waterbearfieldschool/diy-phone/oldbranch/v24/p26.py

# SPDX-FileCopyrightText: 2021 ladyada for Adafruit Industries
# SPDX-License-Identifier: MIT

"""
This test will initialize the display using displayio and draw a solid green
background, a smaller purple rectangle, and some yellow text.
"""
import time
import adafruit_sdcard
import board
import displayio
import digitalio
import storage
import terminalio
import busio
from adafruit_display_text import label
from fourwire import FourWire
from adafruit_bus_device.i2c_device import I2CDevice
from adafruit_st7789 import ST7789
import supervisor
supervisor.runtime.autoreload = False


address_book = [["Don (voip)",16512524765],["Don (iphone)",17813230341],["Liz",16174299144]]

recipient_index=0
recipient=address_book[recipient_index]

# Address book functions
def save_address_book():
    try:
        with open("/sd/addressbook.txt", "w") as f:
            for entry in address_book:
                f.write(f"{entry[0]},{entry[1]}\n")
        pass  # Address book saved
    except Exception as e:
        pass  # Error saving address book

def load_address_book():
    global address_book
    try:
        with open("/sd/addressbook.txt", "r") as f:
            address_book = []
            for line in f.readlines():
                if line.strip():
                    parts = line.strip().split(',')
                    if len(parts) == 2:
                        name = parts[0]
                        number = int(parts[1])
                        address_book.append([name, number])
        pass  # Address book loaded
    except Exception as e:
        pass  # Error loading address book, using defaults
        # Create default address book file
        save_address_book()

def lookup_contact_name(phone_number):
    # Clean phone number for comparison
    clean_number = str(phone_number).replace('+', '').replace('-', '').replace(' ', '')
    
    for entry in address_book:
        contact_number = str(entry[1]).replace('+', '').replace('-', '').replace(' ', '')
        if clean_number.endswith(contact_number) or contact_number.endswith(clean_number):
            return entry[0]
    
    # Return formatted phone number if not found
    if clean_number.startswith('1') and len(clean_number) == 11:
        return f"+1 {clean_number[1:4]}-{clean_number[4:7]}-{clean_number[7:]}"
    elif len(clean_number) == 10:
        return f"{clean_number[:3]}-{clean_number[3:6]}-{clean_number[6:]}"
    else:
        return clean_number

# Removed search_contacts function - no longer needed

spi = busio.SPI(board.SCK, board.MOSI, board.MISO)
cs = digitalio.DigitalInOut(board.D10)

sdcard = adafruit_sdcard.SDCard(spi, cs)
vfs = storage.VfsFat(sdcard)
storage.mount(vfs, "/sd")
    
with open("/sd/test.txt", "w") as f:
    f.write("Hello world!\r\n")

with open("/sd/test.txt", "r") as f:
    pass  # File test
    
    
# Release any resources currently in use for the displays
displayio.release_displays()

#spi = board.SPI()
spi = busio.SPI(clock=board.A2, MOSI=board.A0, MISO=board.A1)
tft_cs = board.A3
tft_dc = board.A5

display_bus = FourWire(spi, command=tft_dc, chip_select=tft_cs, reset=board.D12)

display = ST7789(display_bus, width=320, height=240, rotation=90)

# Make the display context
splash = displayio.Group()
display.root_group = splash

#color_bitmap = displayio.Bitmap(320, 240, 1)
#color_palette = displayio.Palette(1)
#color_palette[0] = 0x00FF00  # Bright Green

#bg_sprite = displayio.TileGrid(color_bitmap, #pixel_shader=color_palette, x=0, y=0)
#splash.append(bg_sprite)

# Draw a smaller inner rectangle
#inner_bitmap = displayio.Bitmap(280, 200, 1)
#inner_palette = displayio.Palette(1)
#inner_palette[0] = 0xAA0088  # Purple
#inner_sprite = displayio.TileGrid(inner_bitmap, #pixel_shader=inner_palette, x=20, y=20)
#splash.append(inner_sprite)

# Draw a label
#text_group = displayio.Group(scale=1, x=57, y=120)
#text = "Hello World!"
#text_area = label.Label(terminalio.FONT, text=text, color=0xFFFF00)
#text_group.append(text_area)  # Subgroup for text scaling
#splash.append(text_group)

#recipient_area = label.Label(terminalio.FONT, text="", color=0xFFFF00, x=5, y=5)

# Inbox view elements
inbox_title = label.Label(terminalio.FONT, text="INBOX", color=0x00FF00, scale=2, x=5, y=10)
status_area = label.Label(terminalio.FONT, text="", color=0xFFFF00, scale=1, x=5, y=220)
info_area = label.Label(terminalio.FONT, text="", color=0x888888, scale=1, x=5, y=230)

# Message list lines (showing multiple messages in inbox view)
msg_line1 = label.Label(terminalio.FONT, text="", color=0xFFFF00, scale=1, x=5, y=35)
msg_line2 = label.Label(terminalio.FONT, text="", color=0xFFFF00, scale=1, x=5, y=50)  
msg_line3 = label.Label(terminalio.FONT, text="", color=0xFFFF00, scale=1, x=5, y=65)
msg_line4 = label.Label(terminalio.FONT, text="", color=0xFFFF00, scale=1, x=5, y=80)
msg_line5 = label.Label(terminalio.FONT, text="", color=0xFFFF00, scale=1, x=5, y=95)
msg_line6 = label.Label(terminalio.FONT, text="", color=0xFFFF00, scale=1, x=5, y=110)
msg_line7 = label.Label(terminalio.FONT, text="", color=0xFFFF00, scale=1, x=5, y=125)
msg_line8 = label.Label(terminalio.FONT, text="", color=0xFFFF00, scale=1, x=5, y=140)

# Detail view elements (hidden initially)
detail_from = label.Label(terminalio.FONT, text="", color=0x00FF00, scale=1, x=5, y=35)
detail_time = label.Label(terminalio.FONT, text="", color=0x888888, scale=1, x=5, y=50)
detail_content1 = label.Label(terminalio.FONT, text="", color=0xFFFF00, scale=1, x=5, y=70)
detail_content2 = label.Label(terminalio.FONT, text="", color=0xFFFF00, scale=1, x=5, y=85)
detail_content3 = label.Label(terminalio.FONT, text="", color=0xFFFF00, scale=1, x=5, y=100)
detail_content4 = label.Label(terminalio.FONT, text="", color=0xFFFF00, scale=1, x=5, y=115)
detail_content5 = label.Label(terminalio.FONT, text="", color=0xFFFF00, scale=1, x=5, y=130)
detail_actions = label.Label(terminalio.FONT, text="", color=0x00FF00, scale=1, x=5, y=155)

# Compose view elements  
compose_title = label.Label(terminalio.FONT, text="", color=0x00FF00, scale=1, x=5, y=35)
compose_content = label.Label(terminalio.FONT, text="", color=0xFFFF00, scale=1, x=5, y=55)

msg_lines = [msg_line1, msg_line2, msg_line3, msg_line4, msg_line5, msg_line6, msg_line7, msg_line8]
detail_lines = [detail_from, detail_time, detail_content1, detail_content2, detail_content3, detail_content4, detail_content5, detail_actions]
compose_lines = [compose_title, compose_content]

# Add all elements to splash
splash.append(inbox_title)
splash.append(status_area)
splash.append(info_area)

for line in msg_lines:
    splash.append(line)
for line in detail_lines: 
    splash.append(line)
for line in compose_lines:
    splash.append(line)

i2c = board.I2C()

#while not i2c.try_lock():
#    pass
    
#i2c_devices=i2c.scan()
#print(i2c_devices)

#cardkb=95

kb = I2CDevice(i2c, 0x5F)

from adafruit_ticks import ticks_ms, ticks_add, ticks_diff, ticks_less

uart = busio.UART(board.D2, board.A4, baudrate=115200,timeout=0,receiver_buffer_size=5024)

ESC = chr(27)
NUL = '\x00'
CR = "\r"
LF = "\n"
TAB = bytearray(b'\x09')
LEFT = bytearray(b'\xB4')
RIGHT = bytearray(b'\xB7')
DOWN = bytearray(b'\xB6')
UP = bytearray(b'\xB5')
BACK = bytearray(b'\x08')
# Add new keys for inbox navigation
ENTER_KEY = bytearray(b'\r')  # For selecting message
B_KEY = b'b'  # For back
R_KEY = b'r'  # For reply
C_KEY = b'c'  # For compose
N_KEY = b'n'  # For new number entry / get new messages
D_KEY = b'd'  # For delete all from SIM
SPACE_KEY = b' '  # For call screen
DEL_KEY = bytearray(b'\x7f')  # For delete
c = ''
b = bytearray(1)

instr = ''
radio_instr = ''

def parse_sms_message(line):
    if not line.startswith('+CMGL:'):
        return None
    
    try:
        # Parse: +CMGL: index,"status","sender","","timestamp"
        parts = line.split(',')
        
        index = parts[0].split(':')[1].strip()
        status = parts[1].strip().strip('"')
        sender = parts[2].strip().strip('"') 
        
        # Reconstruct timestamp from parts 4 and 5 (it got split by comma)
        timestamp_part1 = parts[4].strip().strip('"')  # "25/12/25"
        timestamp_part2 = parts[5].strip().strip('"')  # "16:25:06-32"
        timestamp = timestamp_part1 + ',' + timestamp_part2
        
        # Convert timestamp to filename-safe format: YYMMDD_HHMMSS
        # From: "25/12/25,16:25:06-32" to: "251225_162506"
        date_part, time_part = timestamp.split(',')
        time_clean = time_part.split('-')[0]
        file_timestamp = date_part.replace('/', '') + '_' + time_clean.replace(':', '')
        
        result = {
            'index': index,
            'status': status, 
            'sender': sender,
            'timestamp': timestamp,
            'file_id': file_timestamp
        }
        return result
    except Exception as e:
        pass  # Error parsing SMS
        return None

def store_sms_to_sd(sms_data, content):
    try:
        filename = f"/sd/sms_{sms_data['file_id']}.txt"
        with open(filename, "w") as f:
            f.write(f"From: {sms_data['sender']}\n")
            f.write(f"Time: {sms_data['timestamp']}\n") 
            f.write(f"Status: {sms_data['status']}\n")
            f.write(f"Content: {content}\n")
        pass  # SMS stored
        return True
    except Exception as e:
        pass  # Error storing SMS
        return False

def load_sms_from_sd(force_reload=False):
    
    sms_list = []
    
    # Try different approaches to find SMS files
    try:
        import os
        files = os.listdir("/sd")
        pass
    except:
        pass  # Manual scan fallback
        # Manual file discovery for CircuitPython
        files = []
        # Try common timestamp patterns based on recent dates
        base_patterns = ["251225", "251226", "251227", "251228", "251229", "251230", "251231"]
        time_patterns = []
        for hour in range(24):
            for minute in range(0, 60, 5):  # Check every 5 minutes
                time_patterns.append(f"{hour:02d}{minute:02d}")
        
        for date in base_patterns[:3]:  # Only check last 3 days
            for time in time_patterns[:20]:  # Reduce to 20 checks
                filename = f"sms_{date}_{time}*.txt"
                try:
                    # Try to open the file to see if it exists
                    test_name = f"sms_{date}_{time}00.txt"
                    with open(f"/sd/{test_name}", "r") as f:
                        files.append(test_name)
                        pass  # Found SMS file
                except:
                    continue
                    
    # Process found files
    for filename in files:
        if filename.startswith("sms_") and filename.endswith(".txt"):
            try:
                filepath = f"/sd/{filename}"
                pass  # Trying to load file
                with open(filepath, "r") as f:
                    lines = f.readlines()
                    if len(lines) >= 4:
                        sms_data = {
                            'filename': filename,
                            'sender': lines[0].strip().replace('From: ', ''),
                            'time': lines[1].strip().replace('Time: ', ''),
                            'status': lines[2].strip().replace('Status: ', ''),
                            'content': lines[3].strip().replace('Content: ', '')
                        }
                        sms_list.append(sms_data)
                        pass  # Successfully loaded
                    else:
                        pass  # Invalid SMS file format
            except Exception as file_error:
                pass  # Error reading file
                
    # Sort by filename (which includes timestamp) - most recent first
    sms_list.sort(key=lambda x: x['filename'], reverse=True)
    
    # Limit to 20 most recent messages to save memory
    if len(sms_list) > 20:
        sms_list = sms_list[:20]
    
    return sms_list

# Global buffer for accumulating SMS notifications
sms_notification_buffer = ""

# Global UART buffer for complete line reading
uart_line_buffer = ""

def read_uart_lines():
    """Read UART data and return complete lines, buffering incomplete data"""
    global uart_line_buffer
    
    if uart.in_waiting > 0:
        # Read all available data
        new_data = uart.read(uart.in_waiting)
        if new_data:
            try:
                # Add to buffer
                uart_line_buffer += new_data.decode()
                
                # Extract complete lines
                lines = []
                while '\r\n' in uart_line_buffer:
                    line, uart_line_buffer = uart_line_buffer.split('\r\n', 1)
                    if line:  # Don't add empty lines
                        lines.append(line)
                
                return lines
                
            except Exception as e:
                print(f"Error reading UART: {e}")
                return []
    
    return []

def handle_incoming_sms_notification(data):
    """Handle +CMTI notification for new incoming SMS"""
    global sms_notification_buffer
    
    try:
        # Decode without keyword arguments (CircuitPython compatibility)
        data_str = data.decode()
        pass  # SMS notification received
        
        # Accumulate data in buffer since notifications can be split
        sms_notification_buffer += data_str
        pass  # Buffer updated
        
        # Check if we have a complete CMTI notification 
        # Look for the reassembled +CMTI pattern with comma and line ending
        if ('CMTI:' in sms_notification_buffer or '+CMTI:' in sms_notification_buffer) and ',' in sms_notification_buffer and '\r\n' in sms_notification_buffer:
            print("Found complete CMTI notification")
            
            # Try to find and reconstruct the CMTI line
            buffer_clean = sms_notification_buffer.replace('\r\n', ' ').replace('\r', ' ').replace('\n', ' ')
            
            # Look for the CMTI pattern - might be split as +C MTI: or +CMTI:
            if 'MTI:' in buffer_clean:
                # Find the MTI: part and reconstruct
                parts = buffer_clean.split()
                cmti_line = None
                
                for i, part in enumerate(parts):
                    if 'MTI:' in part:
                        # Try to reconstruct +CMTI: line
                        if i > 0 and parts[i-1].endswith('+C'):
                            # Case: ['+C', 'MTI:', '"SM",9']
                            cmti_line = '+CMTI: ' + ' '.join(parts[i+1:])
                        elif part.startswith('+') or part.startswith('MTI:'):
                            # Case: ['MTI:', '"SM",9'] or ['+MTI:', '"SM",9']
                            if part.startswith('MTI:'):
                                cmti_line = '+C' + part + ' ' + ' '.join(parts[i+1:])
                            else:
                                cmti_line = part + ' ' + ' '.join(parts[i+1:])
                        break
                
                if cmti_line and ',' in cmti_line:
                    pass  # Reconstructed CMTI
                    process_cmti_line(cmti_line)
                    sms_notification_buffer = ""  # Clear after processing
                else:
                    print("Could not reconstruct valid CMTI line")
            else:
                print("No MTI pattern found in buffer")
                
    except Exception as e:
        pass  # Error handling SMS notification

def process_cmti_line(line):
    """Process a complete +CMTI line"""
    try:
        # Parse: +CMTI: "SM",6
        if ':' in line and ',' in line:
            # Split by comma to get the index
            parts = line.split(',')
            if len(parts) >= 2:
                try:
                    # Extract number from second part, removing quotes and whitespace
                    index_part = parts[1].strip().strip('"').strip()
                    message_index = int(index_part)
                    pass  # New SMS at index
                    
                    # Auto-retrieve the new message
                    retrieve_new_message(message_index)
                    
                except ValueError as ve:
                    pass  # Could not parse message index
                    # Fallback: get all messages
                    auto_get_all_messages()
            else:
                pass  # Unexpected CMTI format
                auto_get_all_messages()
        else:
            pass  # Invalid CMTI line format
            
    except Exception as e:
        pass  # Error processing CMTI line

def retrieve_new_message(message_index):
    """Retrieve a specific message by index"""
    try:
        pass  # Retrieving message
        
        # Set text mode
        uart.write(bytes('AT+CMGF=1\r',"ascii"))
        time.sleep(.2)
        uart.read(uart.in_waiting)  # Clear response
        
        # Read the specific message
        uart.write(bytes(f'AT+CMGR={message_index}\r',"ascii"))
        time.sleep(.5)
        data = uart.read(uart.in_waiting).decode()
        pass  # Message response
        
        # Parse and store the message if valid
        lines = data.split('\r\n')
        current_sms = None
        
        for i, line in enumerate(lines):
            if line.startswith('+CMGR:'):
                # Parse message header: +CMGR: "REC UNREAD","+16512524765","","25/12/26,10:30:15-32"
                current_sms = parse_cmgr_message(line)
                pass  # Parsed message header
            elif current_sms and line.strip() and not line.startswith('AT') and not line.startswith('OK'):
                # This is the message content
                if store_sms_to_sd(current_sms, line.strip()):
                    pass  # Stored new message
                    pass  # Cache removed for memory optimization
                    
                    # Update display if in inbox view
                    if current_view == "inbox":
                        refresh_inbox_highlighting()
                        
                break
                
    except Exception as e:
        pass  # Error retrieving message
        # Fallback: get all messages
        auto_get_all_messages()

def parse_cmgr_message(line):
    """Parse +CMGR response format"""
    try:
        pass  # Parsing CMGR line
        # Parse: +CMGR: "REC UNREAD","+16512524765","","25/12/25","17:48:42-32"
        parts = line.split(',')
        pass  # CMGR parts parsed
        
        if len(parts) >= 5:
            status = parts[0].split(':')[1].strip().strip('"')
            sender = parts[1].strip().strip('"')
            # Skip parts[2] (usually empty "")
            
            # Reconstruct timestamp from parts 3 and 4 (it gets split by comma)
            timestamp_part1 = parts[3].strip().strip('"')  # "25/12/25"
            timestamp_part2 = parts[4].strip().strip('"')  # "17:48:42-32"
            timestamp = timestamp_part1 + ',' + timestamp_part2
            
            pass  # Extracted CMGR data
            
            # Convert timestamp to filename-safe format
            if ',' in timestamp:
                date_part, time_part = timestamp.split(',')
                time_clean = time_part.split('-')[0]
                file_timestamp = date_part.replace('/', '') + '_' + time_clean.replace(':', '')
            else:
                # Fallback if timestamp format is unexpected
                import time as time_mod
                file_timestamp = str(int(time_mod.time()))
                
            result = {
                'index': 'auto',
                'status': status,
                'sender': sender,
                'timestamp': timestamp,
                'file_id': file_timestamp
            }
            pass  # Created CMGR result
            return result
        elif len(parts) >= 4:
            # Fallback for cases where timestamp might not be split
            status = parts[0].split(':')[1].strip().strip('"')
            sender = parts[1].strip().strip('"')
            timestamp = parts[3].strip().strip('"')
            
            pass  # Extracted CMGR data (fallback)
            
            # Convert timestamp to filename-safe format
            if ',' in timestamp:
                date_part, time_part = timestamp.split(',')
                time_clean = time_part.split('-')[0]
                file_timestamp = date_part.replace('/', '') + '_' + time_clean.replace(':', '')
            else:
                # Fallback if timestamp format is unexpected
                import time as time_mod
                file_timestamp = str(int(time_mod.time()))
                
            result = {
                'index': 'auto',
                'status': status,
                'sender': sender,
                'timestamp': timestamp,
                'file_id': file_timestamp
            }
            pass  # Created CMGR result (fallback)
            return result
        else:
            pass  # Insufficient CMGR parts
            return None
            
    except Exception as e:
        pass  # Error parsing CMGR message
        return None

def auto_get_all_messages():
    """Automatically get all messages (fallback for notification parsing errors)"""
    pass  # Auto-retrieving all messages
    get_messages()
    if current_view == "inbox":
        display_inbox()  # Force full refresh

def delete_all_messages():
    uart.write(bytes('AT+CMGF=1\r',"ascii"))
    time.sleep(.2)
    uart.write(bytes('AT+CMGDA="DEL ALL"\r',"ascii"))
    time.sleep(.5)
    data=uart.read(uart.in_waiting).decode()
    print("Delete result:", data)

def network_status():
    uart.write(bytes('AT+CSQ\r',"ascii"))
    time.sleep(.2)
    data=uart.read(uart.in_waiting).decode()
    pass

def get_messages():
    status_area.text='(checking messages...)'
    pass
    uart.write(bytes('AT+CMGF=1\r',"ascii"))
    time.sleep(.2)
    data=uart.read(uart.in_waiting)
    pass
    
    uart.write(bytes('AT+CMGL=\"ALL\"\r',"ascii"))
    time.sleep(.3)
    data=uart.read(uart.in_waiting).decode()
    pass
    
    # Parse and store new SMS messages
    lines = data.split('\r\n')
    current_sms = None
    messages_stored = 0
    
    for i, line in enumerate(lines):
        if line.startswith('+CMGL:'):
            current_sms = parse_sms_message(line)
        elif current_sms and line.strip() and not line.startswith('AT') and not line.startswith('OK'):
            # This is the message content
            if store_sms_to_sd(current_sms, line.strip()):
                messages_stored += 1
            current_sms = None
    
    pass  # Total messages stored
    if messages_stored > 0:
        pass  # Cache removed for memory optimization
    status_area.text=''
    
    # Refresh inbox display after loading messages
    if current_view == "inbox":
        import gc
        gc.collect()  # Force garbage collection
        display_inbox()

# Global variables for inbox navigation  
current_view = "inbox"  # "inbox", "detail", "compose", "select_recipient", "thread"
selected_message_index = 0
inbox_scroll_offset = 0
compose_message = ""
selected_recipient_index = 0
manual_number_entry = ""
recipient_mode = "contacts"  # "contacts" or "manual"

# Call view variables
call_selected_index = 0
call_manual_number = ""
call_mode = "contacts"  # "contacts" or "manual"
call_in_progress = False
call_status = ""  # "dialing", "connected", "ended", "failed"
call_contact_name = ""
call_start_time = 0
call_end_countdown = 0
call_duration_counter = 0
call_connect_time = 0  # Actual time when call connected
call_next_update = 0  # Next time to update display (1 second intervals)

# Incoming call variables
incoming_call_active = False
incoming_call_answered = False
incoming_caller_number = None
last_clip_caller_id = None  # Store caller ID from most recent +CLIP
ring_detected_time = 0  # Time when first RING was detected

# Thread view variables
thread_messages = []
thread_contact = ""
thread_scroll_offset = 0
thread_selected_index = 0

# Minimal thread cache for functionality (memory optimized)
cached_thread_lines = []
thread_cache_valid = False
thread_cache_contact = ""
thread_message_line_map = []

def hide_all_views():
    # Hide inbox view
    for line in msg_lines:
        line.text = ""
    
    # Hide detail view  
    for line in detail_lines:
        line.text = ""
        
    # Hide compose view
    for line in compose_lines:
        line.text = ""
    
    # Clear info area when switching views
    info_area.text = ""

def format_sender(sender):
    # Use contact name if available, otherwise format phone number
    contact_name = lookup_contact_name(sender)
    if len(contact_name) > 10:  # Truncate long names
        return contact_name[:8] + ".."
    return contact_name

def format_timestamp(timestamp):
    # Convert timestamp to "MM/DD HH:MM" format
    try:
        pass  # Formatting timestamp
        
        # Check if timestamp has time component
        if ',' in timestamp:
            # Full timestamp: "25/12/25,16:25:06-32"
            date_part, time_part = timestamp.split(',')
            time_clean = time_part.split('-')[0][:5]  # HH:MM
        else:
            # Date only: "25/12/25"
            date_part = timestamp
            time_clean = "00:00"  # Default time
            
        # Parse date parts
        date_components = date_part.split('/')
        if len(date_components) == 3:
            # Try different date formats
            if len(date_components[0]) == 2 and len(date_components[2]) == 2:
                # Could be YY/MM/DD or DD/MM/YY
                # Check if first component looks like year (20-30) or day (01-31)
                try:
                    first_num = int(date_components[0])
                    if first_num >= 20 and first_num <= 30:
                        # Likely YY/MM/DD format: "25/12/25" -> year=25, month=12, day=25
                        year, month, day = date_components
                    else:
                        # Likely DD/MM/YY format: "26/12/25" -> day=26, month=12, year=25  
                        day, month, year = date_components
                    
                    return f"{month}/{day} {time_clean}"
                except ValueError:
                    # If parsing numbers fails, use fallback
                    return f"{date_components[1]}/{date_components[0]} {time_clean}"
            else:
                # Fallback: assume middle is month, last is day
                return f"{date_components[1]}/{date_components[2]} {time_clean}"
        else:
            return timestamp[:8]  # Fallback
            
    except Exception as e:
        pass  # Error formatting timestamp
        return timestamp[:8] if len(timestamp) >= 8 else timestamp  # Fallback

def format_content_preview(content, max_length=15):
    # Truncate content for inbox preview (shorter to fit 3 columns)
    if len(content) > max_length:
        return content[:max_length] + "..."
    return content

def display_inbox():
    global selected_message_index, inbox_scroll_offset
    import gc
    gc.collect()  # Clear memory before display operations
    hide_all_views()
    
    # Reset title to INBOX and normalize text scales
    inbox_title.text = "INBOX"
    compose_title.scale = 1
    compose_content.scale = 1
    
    sms_list = load_sms_from_sd()
    
    if not sms_list:
        msg_lines[0].text = "No messages"
        pass  # No messages to display
        return
    
    # Ensure selected index is valid
    if selected_message_index >= len(sms_list):
        selected_message_index = len(sms_list) - 1
    elif selected_message_index < 0:
        selected_message_index = 0
    
    # Adjust scroll offset to keep selected message visible
    if selected_message_index < inbox_scroll_offset:
        inbox_scroll_offset = selected_message_index
    elif selected_message_index >= inbox_scroll_offset + len(msg_lines):
        inbox_scroll_offset = selected_message_index - len(msg_lines) + 1
    
    # Display messages in 3-column format: "From | Time | Content"
    for i, line in enumerate(msg_lines):
        msg_idx = inbox_scroll_offset + i
        if msg_idx < len(sms_list):
            sms = sms_list[msg_idx]
            sender = format_sender(sms['sender'])
            timestamp = format_timestamp(sms['time'])
            content = format_content_preview(sms['content'])
            
            # Format: "NAME     TIME     CONTENT..."
            # Use fixed width columns: 10 chars name, 11 chars time, rest content
            sender_col = sender[:10]  # Pad and truncate to 10 chars
            time_col = timestamp[:8]  # Pad and truncate to 11 chars
            
            # Highlight selected message
            if msg_idx == selected_message_index:
                line.text = ">" + sender_col + " " + time_col + " " + content
                line.color = 0x00FF00  # Green for selected
            else:
                line.text = " " + sender_col + " " + time_col + " " + content
                line.color = 0xFFFF00  # Yellow for normal
        else:
            line.text = ""
    
    status_area.text = f"MSG {selected_message_index + 1}/{len(sms_list)} - UP/DN:nav RIGHT/ENTER:view C:compose N:new D:del"
    info_area.text = "↑↓:select  ENTER:thread  C:compose  SPACE:call  N:refresh  D:del  0-9:dial"

def refresh_inbox_highlighting():
    global selected_message_index, inbox_scroll_offset
    
    # Load SMS data from SD card
    sms_list = load_sms_from_sd()
    
    if not sms_list:
        return
    
    # Ensure selected index is valid
    if selected_message_index >= len(sms_list):
        selected_message_index = len(sms_list) - 1
    elif selected_message_index < 0:
        selected_message_index = 0
    
    # Adjust scroll offset with page up/down behavior
    if selected_message_index < inbox_scroll_offset:
        # Scrolling up beyond top - do page up
        inbox_scroll_offset = max(0, selected_message_index - len(msg_lines) + 1)
    elif selected_message_index >= inbox_scroll_offset + len(msg_lines):
        # Scrolling down beyond bottom - do page down
        inbox_scroll_offset = selected_message_index
    
    # Only update highlighting, don't rebuild content
    for i, line in enumerate(msg_lines):
        msg_idx = inbox_scroll_offset + i
        if msg_idx < len(sms_list):
            sms = sms_list[msg_idx]
            sender = format_sender(sms['sender'])
            timestamp = format_timestamp(sms['time'])
            content = format_content_preview(sms['content'])
            
            # Format: "NAME     TIME     CONTENT..."
            # Use fixed width columns: 10 chars name, 11 chars time, rest content
            sender_col = sender[:10]  # Pad and truncate to 10 chars
            time_col = timestamp[:8]  # Pad and truncate to 11 chars
            
            # Highlight selected message
            if msg_idx == selected_message_index:
                line.text = ">" + sender_col + " " + time_col + " " + content
                line.color = 0x00FF00  # Green for selected
            else:
                line.text = " " + sender_col + " " + time_col + " " + content
                line.color = 0xFFFF00  # Yellow for normal
        else:
            line.text = ""
    
    status_area.text = f"MSG {selected_message_index + 1}/{len(sms_list)} - UP/DN:nav RIGHT/ENTER:view C:compose N:new D:del"
    info_area.text = "↑↓:select  ENTER:thread  C:compose  SPACE:call  N:refresh  D:del  0-9:dial"

def scroll_inbox_up():
    global selected_message_index
    if selected_message_index > 0:
        selected_message_index -= 1
        refresh_inbox_highlighting()

def scroll_inbox_down():
    global selected_message_index
    sms_list = load_sms_from_sd()
    if sms_list and selected_message_index < len(sms_list) - 1:
        selected_message_index += 1
        refresh_inbox_highlighting()

def display_message_detail():
    global current_view, selected_message_index
    current_view = "detail"
    hide_all_views()
    
    sms_list = load_sms_from_sd()
    if not sms_list or selected_message_index >= len(sms_list):
        detail_lines[0].text = "Message not found"
        return
    
    sms = sms_list[selected_message_index]
    
    # Display message details
    detail_from.text = f"From: {sms['sender']}"
    detail_time.text = f"Time: {sms['time']}"
    
    # Wrap content across multiple lines (45 chars per line)
    content = sms['content']
    lines = []
    while content:
        if len(content) <= 45:
            lines.append(content)
            break
        else:
            # Find good break point
            break_point = content.rfind(' ', 0, 45)
            if break_point == -1:
                break_point = 45
            lines.append(content[:break_point])
            content = content[break_point:].strip()
    
    # Display content lines
    content_labels = [detail_content1, detail_content2, detail_content3, detail_content4, detail_content5]
    for i, line_label in enumerate(content_labels):
        if i < len(lines):
            line_label.text = lines[i]
        else:
            line_label.text = ""
    
    detail_actions.text = "R:reply B:back DEL:delete"
    status_area.text = f"MESSAGE DETAIL {selected_message_index + 1}/{len(sms_list)}"
    info_area.text = "R:reply  B/←/ESC:back  DEL:delete"

def display_recipient_selection():
    global current_view, selected_recipient_index, recipient_mode, manual_number_entry
    current_view = "select_recipient"
    hide_all_views()
    
    if recipient_mode == "contacts":
        # Show address book contacts
        compose_title.text = "Select Contact:"
        
        contact_text = ""
        for i, contact in enumerate(address_book[:5]):  # Show up to 5 contacts
            if i == selected_recipient_index:
                contact_text += f"> {contact[0]} ({contact[1]})\n"
            else:
                contact_text += f"  {contact[0]} ({contact[1]})\n"
        
        compose_content.text = contact_text
        status_area.text = "TAB:next ENTER:select N:new# ESC:cancel"
        info_area.text = "TAB:next contact  ENTER:select  N:manual entry  ESC:cancel"
        
    else:  # manual mode
        compose_title.text = "Enter Number:"
        compose_content.text = f"> {manual_number_entry}"
        status_area.text = "Type number, ENTER:select, ESC:cancel"
        info_area.text = "Type phone number  ENTER:select  ESC:cancel  BACK:delete"

def display_compose(reply_to=None):
    global current_view, compose_message
    current_view = "compose" 
    hide_all_views()
    
    # Reset text scales to normal
    compose_title.scale = 1
    compose_content.scale = 1
    
    if reply_to:
        # Check if reply_to is a contact name or phone number
        if any(char.isalpha() for char in reply_to):
            # It's likely a contact name, use as-is
            compose_title.text = f"To: {reply_to}"
        else:
            # It's a phone number, format it
            compose_title.text = f"To: {format_sender(reply_to)}"
        
        compose_content.text = f"> {compose_message}"
        status_area.text = "Type message, ENTER:send ESC:cancel"
        info_area.text = "Type your message  ENTER:send  ESC:cancel  BACK:delete char"
    else:
        # Start with recipient selection for new messages
        display_recipient_selection()

def back_to_inbox():
    global current_view
    current_view = "inbox"
    display_inbox()

def display_thread_view():
    """Display all messages from the selected contact"""
    global current_view, thread_messages, thread_contact, thread_scroll_offset, thread_selected_index
    current_view = "thread"
    hide_all_views()
    
    # Reset text scales to normal
    compose_title.scale = 1
    compose_content.scale = 1
    
    # Get the selected contact from current message
    sms_list = load_sms_from_sd()
    if not sms_list or selected_message_index >= len(sms_list):
        back_to_inbox()
        return
        
    selected_sms = sms_list[selected_message_index]
    thread_contact = selected_sms['sender']
    contact_name = format_sender(thread_contact)
    
    # Find all messages from this contact
    thread_messages = []
    for sms in sms_list:
        if sms['sender'] == thread_contact:
            thread_messages.append(sms)
    
    # Sort by timestamp (filename contains timestamp) - oldest first, newest last
    thread_messages.sort(key=lambda x: x['filename'], reverse=False)
    
    # Find the selected message in the thread
    thread_selected_index = 0
    for i, msg in enumerate(thread_messages):
        if msg['filename'] == selected_sms['filename']:
            thread_selected_index = i
            break
    
    pass  # Thread view info
    
    # Build the thread display cache
    build_thread_cache()
    
    # Calculate initial scroll position to show originally selected message
    calculate_thread_scroll_for_selection()
    
    # Display the thread
    refresh_thread_display()

def build_thread_cache():
    """Build the cached display lines for the thread"""
    global cached_thread_lines, thread_cache_valid, thread_cache_contact, thread_message_line_map
    
    if not thread_messages:
        cached_thread_lines = []
        thread_message_line_map = []
        thread_cache_valid = True
        return
    
    contact_name = format_sender(thread_contact)
    
    # Build all display lines for the thread
    cached_thread_lines = []
    thread_message_line_map = []  # Maps each display line to its message index
    
    for msg_idx, sms in enumerate(thread_messages):
        timestamp = format_timestamp(sms['time'])
        content = sms['content']
        
        # Create lines with timestamp and content on same line, then wrap
        # Format: "MM/DD HH:MM message content continues here..."
        timestamp_width = 11  # "MM/DD HH:MM" is 11 chars
        content_width = 45 - timestamp_width - 1  # Remaining width after timestamp and space
        
        remaining_content = content
        first_line = True
        
        while remaining_content or first_line:
            if first_line:
                # First line: timestamp + beginning of content
                if len(remaining_content) <= content_width:
                    # Content fits on first line
                    line_text = f"{timestamp} {remaining_content}"
                    cached_thread_lines.append(line_text)
                    thread_message_line_map.append(msg_idx)
                    remaining_content = ""
                else:
                    # Content needs wrapping
                    break_point = remaining_content.rfind(' ', 0, content_width)
                    if break_point == -1:
                        break_point = content_width
                    line_content = remaining_content[:break_point]
                    line_text = f"{timestamp} {line_content}"
                    cached_thread_lines.append(line_text)
                    thread_message_line_map.append(msg_idx)
                    remaining_content = remaining_content[break_point:].strip()
                first_line = False
            else:
                # Continuation lines: indented to align with content
                indent = " " * (timestamp_width + 1)  # Match timestamp width + space
                if len(remaining_content) <= content_width:
                    # Remaining content fits on this line
                    line_text = f"{indent}{remaining_content}"
                    cached_thread_lines.append(line_text)
                    thread_message_line_map.append(msg_idx)
                    remaining_content = ""
                else:
                    # Need more wrapping
                    break_point = remaining_content.rfind(' ', 0, content_width)
                    if break_point == -1:
                        break_point = content_width
                    line_content = remaining_content[:break_point]
                    line_text = f"{indent}{line_content}"
                    cached_thread_lines.append(line_text)
                    thread_message_line_map.append(msg_idx)
                    remaining_content = remaining_content[break_point:].strip()
    
    thread_cache_valid = True
    thread_cache_contact = thread_contact
    pass  # Thread cache built

def refresh_thread_display():
    """Refresh the thread view display using cached lines with message highlighting"""
    global thread_contact, thread_scroll_offset, thread_selected_index
    
    if not thread_messages:
        contact_name = format_sender(thread_contact) if thread_contact else "Unknown"
        inbox_title.text = contact_name
        msg_lines[0].text = "No messages in thread"
        return
    
    contact_name = format_sender(thread_contact)
    
    # Update the title at top of screen to just contact name
    inbox_title.text = contact_name
    
    # Clear all message lines
    for line in msg_lines:
        line.text = ""
        line.color = 0xFFFF00
    
    # Use cached thread cache for efficient scrolling
    if not thread_cache_valid or thread_cache_contact != thread_contact:
        build_thread_cache()
    
    # Display lines starting from scroll offset with highlighting
    for i, line in enumerate(msg_lines):
        line_idx = thread_scroll_offset + i
        if line_idx < len(cached_thread_lines):
            line.text = cached_thread_lines[line_idx]
            
            # Highlight lines that belong to the selected message
            msg_idx = thread_message_line_map[line_idx]
            if msg_idx == thread_selected_index:
                line.color = 0x00FF00  # Green for selected message
            else:
                line.color = 0xFFFF00  # Yellow for normal
        else:
            line.text = ""
    
    # Calculate how many total "pages" of content we have
    total_lines = len(cached_thread_lines)
    visible_lines = len(msg_lines)
    max_scroll = max(0, total_lines - visible_lines)
    
    status_area.text = f"MSG {thread_selected_index + 1}/{len(thread_messages)} - UP/DN:nav ENTER:view R:reply B:back"
    info_area.text = "↑↓:select  ENTER:view  R:reply  B/←/ESC:back"

def calculate_thread_scroll_for_selection():
    """Calculate scroll offset to show the selected message"""
    global thread_scroll_offset, thread_selected_index
    
    if not thread_message_line_map or thread_selected_index >= len(thread_messages):
        return
    
    # Find the first line of the selected message
    selected_line = None
    for line_idx, msg_idx in enumerate(thread_message_line_map):
        if msg_idx == thread_selected_index:
            selected_line = line_idx
            break
    
    if selected_line is not None:
        # Adjust scroll to show selected message, preferably near middle of screen
        middle_offset = len(msg_lines) // 2
        thread_scroll_offset = max(0, selected_line - middle_offset)
        
        # Ensure we don't scroll past the end
        max_scroll = max(0, len(cached_thread_lines) - len(msg_lines))
        thread_scroll_offset = min(thread_scroll_offset, max_scroll)

def calculate_thread_scroll_to_bottom():
    """Calculate scroll offset to show the most recent message at the bottom of screen"""
    global thread_scroll_offset, thread_selected_index
    
    if not cached_thread_lines:
        thread_scroll_offset = 0
        return
    
    # Calculate scroll to show most recent content at bottom
    total_lines = len(cached_thread_lines)
    visible_lines = len(msg_lines)
    
    if total_lines <= visible_lines:
        # All content fits on screen, no scrolling needed
        thread_scroll_offset = 0
        # Set selection to the most recent message (last message, index -1)
        thread_selected_index = len(thread_messages) - 1
    else:
        # Scroll to show bottom content
        thread_scroll_offset = total_lines - visible_lines
        # Set selection to the most recent message (last message, index -1)
        thread_selected_index = len(thread_messages) - 1

def scroll_thread_up():
    global thread_selected_index
    if thread_selected_index > 0:
        thread_selected_index -= 1
        calculate_thread_scroll_for_selection()
        refresh_thread_display()

def scroll_thread_down():
    global thread_selected_index
    if thread_messages and thread_selected_index < len(thread_messages) - 1:
        thread_selected_index += 1
        calculate_thread_scroll_for_selection()
        refresh_thread_display()

def view_thread_message():
    """View the selected message in thread view"""
    global selected_message_index
    if thread_messages and thread_selected_index < len(thread_messages):
        # Find the original message index in the main sms list
        selected_msg = thread_messages[thread_selected_index]
        sms_list = load_sms_from_sd()
        for i, sms in enumerate(sms_list):
            if sms['filename'] == selected_msg['filename']:
                selected_message_index = i
                break
        display_message_detail()

def reply_to_thread_contact():
    """Reply to the thread contact"""
    global compose_message
    if thread_contact:
        compose_message = ""
        display_compose(reply_to=thread_contact)

def start_reply():
    global compose_message
    sms_list = load_sms_from_sd()
    if sms_list and selected_message_index < len(sms_list):
        sms = sms_list[selected_message_index]
        compose_message = ""
        display_compose(reply_to=sms['sender'])

def start_new_compose():
    global compose_message, selected_recipient_index, recipient_mode, manual_number_entry
    compose_message = ""
    selected_recipient_index = 0
    recipient_mode = "contacts"
    manual_number_entry = ""
    display_compose()

def select_recipient():
    global current_view, compose_message, recipient_mode, manual_number_entry
    
    if recipient_mode == "contacts":
        if selected_recipient_index < len(address_book):
            selected_contact = address_book[selected_recipient_index]
            compose_message = ""
            # Properly transition to compose mode with selected contact
            display_compose(reply_to=selected_contact[0])
    else:  # manual mode
        if manual_number_entry.strip():
            compose_message = ""
            display_compose(reply_to=manual_number_entry.strip())

def cycle_recipient():
    global selected_recipient_index
    if recipient_mode == "contacts":
        selected_recipient_index = (selected_recipient_index + 1) % len(address_book)
        display_recipient_selection()

def switch_to_manual_entry():
    global recipient_mode, manual_number_entry, selected_recipient_index
    recipient_mode = "manual"
    manual_number_entry = ""
    selected_recipient_index = 0
    display_recipient_selection()

def send_reply():
    global compose_message, current_view
    if current_view == "compose":
        # Extract recipient number from compose_title
        title = compose_title.text
        if "To: " in title:
            recipient_name = title.replace("To: ", "")
            
            # Find the number for this contact
            recipient_number = None
            if "Reply to:" in title:
                # For replies, get from original message
                sms_list = load_sms_from_sd()
                if sms_list and selected_message_index < len(sms_list):
                    sms = sms_list[selected_message_index]
                    recipient_number = sms['sender'].replace('+', '')
            else:
                # Check if it's a number (manual entry) or contact name
                if recipient_name.isdigit() or ('+' in recipient_name):
                    # It's a phone number
                    recipient_number = recipient_name.replace('+', '').replace('-', '').replace(' ', '')
                else:
                    # For new messages, find in address book
                    for contact in address_book:
                        if contact[0] == recipient_name:
                            recipient_number = str(contact[1])
                            break
            
            if recipient_number:
                status_area.text = "Sending..."
                send_message(recipient_number, compose_message)
                compose_message = ""
                back_to_inbox()
            else:
                status_area.text = "Error: No number found"

def display_call_screen():
    """Display the call screen with address book contacts"""
    global current_view, call_selected_index, call_mode, call_manual_number
    current_view = "call"
    hide_all_views()
    
    # Set main title to CALL
    inbox_title.text = "CALL"
    
    if call_mode == "contacts":
        # Show address book contacts for calling
        compose_title.text = "Select Contact:"
        
        contact_text = ""
        for i, contact in enumerate(address_book[:7]):  # Show up to 7 contacts
            if i == call_selected_index:
                contact_text += f"> {contact[0]} ({contact[1]})\n"
            else:
                contact_text += f"  {contact[0]} ({contact[1]})\n"
        
        compose_content.text = contact_text
        status_area.text = "Select contact to call"
        info_area.text = "↑↓:select  ENTER:call  0-9:manual  ESC:cancel"
        
    else:  # manual mode
        compose_title.text = "Enter Number:"
        compose_content.text = f"> {call_manual_number}"
        status_area.text = "Enter phone number to call"
        info_area.text = "Type number  ENTER:call  ESC:cancel  BACK:delete"

def cycle_call_contact_up():
    global call_selected_index
    if call_selected_index > 0:
        call_selected_index -= 1
        display_call_screen()

def cycle_call_contact_down():
    global call_selected_index
    if call_selected_index < len(address_book) - 1:
        call_selected_index += 1
        display_call_screen()

def switch_to_manual_call_entry():
    global call_mode, call_manual_number, call_selected_index
    call_mode = "manual"
    call_manual_number = ""
    call_selected_index = 0
    display_call_screen()

def make_selected_call():
    global call_mode, call_selected_index, call_manual_number
    global call_in_progress, call_status, call_contact_name, call_start_time
    
    if call_mode == "contacts":
        if call_selected_index < len(address_book):
            selected_contact = address_book[call_selected_index]
            phone_number = str(selected_contact[1])
            call_contact_name = selected_contact[0]
            start_monitored_call(phone_number, call_contact_name)
    else:  # manual mode
        if call_manual_number.strip():
            phone_number = call_manual_number.strip()
            call_contact_name = phone_number
            start_monitored_call(phone_number, phone_number)

def start_monitored_call(phone_number, display_name):
    """Start a call and begin monitoring its status"""
    global call_in_progress, call_status, call_contact_name, call_start_time, call_connect_time, call_next_update
    
    call_in_progress = True
    call_status = "dialing"
    call_contact_name = display_name
    call_start_time = 0  # Will be set when call connects
    call_connect_time = 0  # Will be set when call connects
    call_next_update = 0  # Will be set when call connects
    
    # Update display to show calling status
    update_call_status_display()
    
    # Initiate the call
    make_call(phone_number)

def update_call_status_display():
    """Update the call screen to show current call status"""
    global call_in_progress, call_status, call_contact_name
    
    if not call_in_progress:
        return
    
    # Update display based on call status
    # Set main title to CALL for all call states
    inbox_title.text = "CALL"
    
    if call_status == "dialing":
        # Large contact name for dialing
        compose_title.text = call_contact_name
        compose_title.scale = 2  # Make contact name large
        compose_content.text = "Dialing..."
        status_area.text = "Connecting call"
        info_area.text = "Connecting... ESC:hangup"
    elif call_status == "connected":
        call_duration = int(call_start_time) if call_start_time > 0 else 0
        # Large contact name and duration for active call
        compose_title.text = call_contact_name
        compose_title.scale = 2  # Make contact name large
        compose_content.text = str(call_duration) + "s"
        compose_content.scale = 2  # Make duration large
        status_area.text = "Call in progress"
        info_area.text = "Call connected - ESC:hangup"
    elif call_status == "ended":
        call_duration = int(call_start_time) if call_start_time > 0 else 0
        # Reset to normal scale and show call ended info
        compose_title.scale = 1
        compose_content.scale = 1
        compose_title.text = "CALL ENDED: " + call_contact_name
        if call_duration > 0:
            compose_content.text = "Call finished\nNo carrier detected"
        else:
            compose_content.text = "Call finished\nNo carrier detected"
        status_area.text = "Call ended"
        info_area.text = "Returning to inbox in a moment..."
    elif call_status == "failed":
        # Reset to normal scale and show call failed info
        compose_title.scale = 1
        compose_content.scale = 1
        compose_title.text = "CALL FAILED: " + call_contact_name
        compose_content.text = "Call could not connect\nBusy or network error"
        status_area.text = "Call failed"
        info_area.text = "Returning to inbox in a moment..."

def parse_caller_id(clip_line):
    """Parse +CLIP response to extract caller number"""
    try:
        print("Parsing CLIP line: " + clip_line)
        # Parse: +CLIP: "+16512524765",145,"",0,,0
        if '+CLIP:' in clip_line:
            parts = clip_line.split(',')
            print("CLIP parts: " + str(len(parts)))
            if len(parts) >= 1:
                # Extract the phone number (first part after +CLIP:)
                phone_part = parts[0].split(':')[1].strip()
                print("Phone part: " + phone_part)
                # Remove quotes
                phone_number = phone_part.strip('"').strip("'")
                print("Parsed phone number: " + phone_number)
                return phone_number
    except Exception as e:
        print("Error parsing CLIP: " + str(e))
    return None

def lookup_contact_by_number(phone_number):
    """Look up contact name by phone number in address book"""
    if not phone_number:
        print("No phone number to lookup")
        return None
    
    print("Looking up number: " + phone_number)
    # Clean the phone number for comparison (remove +1, spaces, etc.)
    clean_number = phone_number.replace('+1', '').replace(' ', '').replace('(', '').replace(')', '').replace('-', '')
    print("Cleaned number: " + clean_number)
    
    for contact in address_book:
        # Convert contact number to string first, then clean it
        contact_number_str = str(contact[1])
        contact_number = contact_number_str.replace('+1', '').replace(' ', '').replace('(', '').replace(')', '').replace('-', '')
        print("Checking against contact: " + contact[0] + " - " + contact_number)
        if clean_number.endswith(contact_number[-10:]) or contact_number.endswith(clean_number[-10:]):
            print("Found match: " + contact[0])
            return contact[0]  # Return contact name
    
    print("No contact match found")
    return None

def handle_incoming_call(caller_number=None):
    """Handle incoming call display"""
    global current_view, incoming_call_active, call_contact_name
    current_view = "incoming_call"
    incoming_call_active = True
    
    print("Handle incoming call with number: " + str(caller_number))
    
    # Look up caller in address book
    if caller_number:
        contact_name = lookup_contact_by_number(caller_number)
        if contact_name:
            call_contact_name = contact_name
            print("Using contact name: " + contact_name)
        else:
            call_contact_name = caller_number
            print("Using phone number: " + caller_number)
    else:
        call_contact_name = "Unknown Caller"
        print("No caller number provided, using Unknown Caller")
    
    hide_all_views()
    
    # Set main title to CALL
    inbox_title.text = "CALL"
    
    # Show incoming call screen
    compose_title.text = "INCOMING CALL"
    compose_title.scale = 2
    compose_content.text = call_contact_name
    compose_content.scale = 3
    status_area.text = "Incoming call..."
    info_area.text = "ENTER:answer  ESC:reject"
    
    pass  # Incoming call detected

def answer_incoming_call():
    """Answer the incoming call"""
    global incoming_call_active, incoming_call_answered, call_in_progress, call_status
    global call_start_time, call_connect_time, call_next_update
    
    pass  # Answering incoming call
    
    # Send AT command to answer call
    uart.write(bytes('ATA\r', "ascii"))
    time.sleep(0.1)
    
    # Update call state
    incoming_call_active = False
    incoming_call_answered = True
    call_in_progress = True
    call_status = "connected"
    call_start_time = 0
    
    # Record the actual time when call connected
    call_connect_time = ticks_ms()
    call_next_update = ticks_add(call_connect_time, 1000)  # Update every 1000ms (1 second)
    
    update_call_status_display()

def reject_incoming_call():
    """Reject the incoming call"""
    global incoming_call_active, current_view, incoming_caller_number, last_clip_caller_id, ring_detected_time
    
    pass  # Rejecting incoming call
    
    # Send AT command to hang up call
    uart.write(bytes('AT+CHUP\r', "ascii"))
    time.sleep(0.1)
    
    # Return to inbox
    incoming_call_active = False
    incoming_caller_number = None  # Reset caller number
    last_clip_caller_id = None  # Reset stored caller ID
    ring_detected_time = 0  # Reset ring timer
    display_inbox()

def process_call_uart_line(line):
    """Process UART lines related to call status"""
    global call_in_progress, call_status, call_start_time, call_end_countdown, call_duration_counter, call_connect_time, call_next_update
    global incoming_call_active, incoming_caller_number, last_clip_caller_id, ring_detected_time
    
    line_upper = line.upper().strip()
    
    # Check for incoming call (RING)
    if "RING" in line_upper and not call_in_progress and not incoming_call_active:
        import time
        current_time = time.time()
        
        if ring_detected_time == 0:
            # First RING detected - start waiting for +CLIP
            ring_detected_time = current_time
            print("First RING detected, waiting for +CLIP...")
            return True
        elif current_time - ring_detected_time > 0.5:  # Wait 500ms for +CLIP
            # Waited long enough, process the call now
            print("RING timeout, using caller ID: " + str(last_clip_caller_id))
            handle_incoming_call(last_clip_caller_id)
            ring_detected_time = 0  # Reset
            return True
        else:
            # Still waiting for +CLIP
            print("RING detected, still waiting for +CLIP...")
            return True
    
    if not call_in_progress:
        return False  # Not monitoring a call
    
    if "VOICE CALL: BEGIN" in line_upper:
        call_status = "connected"
        call_start_time = 0  # Reset duration counter
        call_duration_counter = 0  # Reset loop counter for duration
        # Record the actual time when call connected
        call_connect_time = ticks_ms()
        call_next_update = ticks_add(call_connect_time, 1000)  # Update every 1000ms (1 second)
        update_call_status_display()
        pass  # Call connected
        return True
        
    elif "VOICE CALL: END" in line_upper:
        global incoming_call_answered, incoming_caller_number, last_clip_caller_id
        call_status = "ended"
        incoming_call_answered = False  # Reset incoming call flag
        incoming_caller_number = None  # Reset caller number
        last_clip_caller_id = None  # Reset stored caller ID
        # Extract call duration if available
        if ":" in line and len(line.split(":")) > 2:
            try:
                duration_part = line.split(":")[-1].strip()
                call_start_time = int(duration_part)
            except:
                pass
        update_call_status_display()
        call_end_countdown = 100  # Show for 10 seconds (30 * 100ms)
        pass  # Call ended
        return True
        
    elif "NO CARRIER" in line_upper:
        if call_status != "ended":  # If we haven't already processed VOICE CALL: END
            global incoming_call_answered, incoming_caller_number, last_clip_caller_id
            call_status = "ended"
            incoming_call_answered = False  # Reset incoming call flag
            incoming_caller_number = None  # Reset caller number
            last_clip_caller_id = None  # Reset stored caller ID
            update_call_status_display()
            call_end_countdown = 100  # Show for 10 seconds
        pass  # No carrier detected
        return True
        
    elif "BUSY" in line_upper or "ERROR" in line_upper:
        call_status = "failed"
        update_call_status_display()
        call_end_countdown = 100  # Show for 10 seconds
        pass  # Call failed
        return True
    
    return False  # Line not related to call status

def end_call_monitoring():
    """End call monitoring and return to inbox"""
    global call_in_progress, call_status, call_end_countdown, incoming_call_answered, incoming_caller_number, last_clip_caller_id, ring_detected_time
    
    # Send hangup command to actually end the call
    uart.write(bytes('AT+CHUP\r',"ascii"))
    time.sleep(0.1)
    
    call_in_progress = False
    call_status = ""
    call_end_countdown = 0
    incoming_call_answered = False
    incoming_caller_number = None  # Reset caller number
    last_clip_caller_id = None  # Reset stored caller ID
    ring_detected_time = 0  # Reset ring timer
    back_to_inbox()

def start_call_screen():
    """Initialize and display the call screen"""
    global call_selected_index, call_mode, call_manual_number
    call_selected_index = 0
    call_mode = "contacts"
    call_manual_number = ""
    display_call_screen()

def delete_current_message():
    global selected_message_index
    sms_list = load_sms_from_sd()
    if sms_list and selected_message_index < len(sms_list):
        sms = sms_list[selected_message_index]
        filename = f"/sd/{sms['filename']}"
        try:
            # Try different ways to delete the file
            try:
                import os
                os.remove(filename)
                pass  # Deleted file
            except:
                # Alternative: overwrite file with empty content
                with open(filename, "w") as f:
                    f.write("")
                pass  # Cleared file
                
            pass  # Cache removed for memory optimization
            
            # Adjust selection after delete
            if selected_message_index >= len(sms_list) - 1:
                selected_message_index = max(0, len(sms_list) - 2)
            back_to_inbox()
        except Exception as e:
            pass  # Error deleting
            status_area.text = "Delete failed"
    
def send_message(recipient,message):
    #ta.text='(sending message...)'
    print("sending message")
    uart.write(bytes('AT+CFUN=1\r',"ascii"))
    time.sleep(.2)
    data=uart.read(uart.in_waiting)
    pass
    #messages.append(data.strip())
    uart.write(bytes('AT+CMGF=1\r',"ascii"))
    time.sleep(.2)
    data=uart.read(uart.in_waiting)
    #messages.append(data.strip())
    pass
    uart.write(bytes('AT+CMGS=\"+'+str(recipient)+'\"\r',"ascii"))
    time.sleep(.5)
    data=uart.read(uart.in_waiting)
    #messages.append(data.strip())
    pass
    uart.write(bytes(message+'\x1a',"ascii"))
    time.sleep(2)
    data=uart.read(uart.in_waiting)
    #print("send result:",data)
    send_result=data.decode().split('\r\n')
    print("send_result=",send_result)

def make_call(recipient):
    
    uart.write(bytes('AT+CNUM\r',"ascii")) # switch to headphones
    time.sleep(.2)
    data=uart.read(uart.in_waiting).decode()
    pass
    
    uart.write(bytes('AT+CSDVC=1\r',"ascii")) # switch to headphones
    time.sleep(.2)
    data=uart.read(uart.in_waiting).decode()
    pass
    
    uart.write(bytes('AT+CLVL=?\r',"ascii")) # query volume range
    time.sleep(.2)
    data=uart.read(uart.in_waiting).decode()
    pass
    
    uart.write(bytes('AT+CLVL=5\r',"ascii")) # set volume to 2
    time.sleep(.2)
    data=uart.read(uart.in_waiting).decode()
    pass
    
    uart.write(bytes('ATD+'+str(recipient)+';\r',"ascii")) # set volume to 2
    time.sleep(2)
    data=uart.read(uart.in_waiting).decode()
    pass
    

# display startup msgs
status_area.text="::starting up::"
#time.sleep(2)
status_area.text=""

# Load address book and start in inbox view
load_address_book()
current_view = "inbox"
display_inbox()

# enable caller id
uart.write(bytes('AT+CLIP=1\r',"ascii")) # set volume to 2
time.sleep(.2)
data=uart.read(uart.in_waiting).decode()

while True:

    # Read complete lines from UART
    uart_lines = read_uart_lines()
    
    # First pass: collect any +CLIP caller ID information
    for line in uart_lines:
        if '+CLIP:' in line.upper():
            last_clip_caller_id = parse_caller_id(line)
            print("Stored caller ID: " + str(last_clip_caller_id))
            
            # If we're waiting for +CLIP after RING, trigger call now
            if ring_detected_time > 0 and not incoming_call_active:
                print("Got +CLIP while waiting, triggering call now")
                handle_incoming_call(last_clip_caller_id)
                ring_detected_time = 0  # Reset
    
    # Second pass: process all other lines including RING
    for line in uart_lines:
        print(uart_lines)
        pass  # UART line received
        
        # Check for call status updates first
        if process_call_uart_line(line):
            continue  # Line was processed as call status
        
        # Check for incoming SMS notification
        if '+CMTI:' in line:
            pass  # Found SMS notification
            # Process the complete CMTI line directly
            process_cmti_line(line)
    #network_status()
    #time.sleep(5)
    #get_messages()

    #recipient=address_book[0]
    #send_message(recipient[1],"hello")
    #print("calling ",recipient[0])
    #make_call(recipient[1])
    #print("sent")
    #time.sleep(60)
    
    #while not i2c.try_lock():
    #    pass
    #i2c.readfrom_into(cardkb,b)
    #i2c.unlock()
    
    with kb:
        kb.readinto(b)
    
    # Handle navigation based on current view
    if current_view == "inbox":
        if (b == UP):
            scroll_inbox_up()
            continue
        if (b == DOWN):
            scroll_inbox_down()
            continue
        if (b == ENTER_KEY) or (b == CR) or (b == RIGHT):
            display_thread_view()
            continue
        if (b == N_KEY):
            get_messages()
            display_inbox()  # Force full refresh after getting new messages
            continue
        if (b == D_KEY):
            delete_all_messages()
            continue
        if (b == C_KEY):
            start_new_compose()
            continue
        if (b == SPACE_KEY):
            start_call_screen()
            continue
        # Handle number keys for direct manual call entry
        c = b.decode() if len(b) == 1 else ''
        if c.isdigit():
            call_manual_number = c  # Start with the pressed digit
            call_mode = "manual"
            call_selected_index = 0
            display_call_screen()
            continue
            
    elif current_view == "detail":
        if (b == B_KEY) or (b == BACK) or (b == LEFT) or (b == ESC):
            back_to_inbox()
            continue
        if (b == R_KEY):
            start_reply()
            continue
        if (b == DEL_KEY):
            delete_current_message()
            continue
            
    elif current_view == "select_recipient":
        if (b == ESC):
            back_to_inbox()
            continue
        if (b == ENTER_KEY) or (b == CR):
            select_recipient()
            continue
        if (b == TAB):
            cycle_recipient()
            continue
        if (b == N_KEY):
            switch_to_manual_entry()
            continue
        if (b == BACK) and recipient_mode == "manual" and len(manual_number_entry) > 0:
            manual_number_entry = manual_number_entry[:-1]
            display_recipient_selection()
            continue
            
    elif current_view == "call":
        if (b == ESC):
            if call_in_progress:
                # Hang up the call
                end_call_monitoring()
            else:
                back_to_inbox()
            continue
        if (b == ENTER_KEY) or (b == CR):
            make_selected_call()
            continue
        if call_mode == "contacts":
            if (b == UP):
                cycle_call_contact_up()
                continue
            if (b == DOWN):
                cycle_call_contact_down()
                continue
            # Handle number keys to switch to manual entry
            c = b.decode() if len(b) == 1 else ''
            if c.isdigit():
                call_manual_number = c
                switch_to_manual_call_entry()
                continue
        else:  # manual mode
            if (b == BACK) and len(call_manual_number) > 0:
                call_manual_number = call_manual_number[:-1]
                display_call_screen()
                continue
            # Handle number and character input
            c = b.decode() if len(b) == 1 else ''
            if c.isdigit() or c in ['+', '-', ' ', '(', ')']:
                call_manual_number += c
                display_call_screen()
                continue
    
    elif current_view == "incoming_call":
        if (b == ENTER_KEY) or (b == CR):
            answer_incoming_call()
            continue
        if (b == ESC):
            reject_incoming_call()
            continue
            
    elif current_view == "thread":
        if (b == UP):
            scroll_thread_up()
            continue
        if (b == DOWN):
            scroll_thread_down()
            continue
        if (b == ENTER_KEY) or (b == CR):
            view_thread_message()
            continue
        if (b == R_KEY):
            reply_to_thread_contact()
            continue
        if (b == B_KEY) or (b == BACK) or (b == LEFT) or (b == ESC):
            back_to_inbox()
            continue
            
    elif current_view == "compose":
        if (b == ESC):
            back_to_inbox()
            continue
        if (b == ENTER_KEY) or (b == CR):
            send_reply()
            continue
        if (b == BACK) and len(compose_message) > 0:
            compose_message = compose_message[:-1]
            display_compose()
            continue
        
    # Handle text input for manual number entry and compose modes
    if current_view == "select_recipient" and recipient_mode == "manual":
        c = b.decode()
        if (c != ESC and c != NUL and c != '\r' and c != '\x08' and c != '\t' and c != 'n'):
            manual_number_entry += c
            display_recipient_selection()
            continue
            
    elif current_view == "compose":
        c = b.decode()
        if (c != ESC and c != NUL and c != '\r' and c != '\x08'):
            compose_message += c
            display_compose()
            continue
    
    # Handle call end countdown
    if call_end_countdown > 0:
        call_end_countdown -= 1
        if call_end_countdown == 0:
            end_call_monitoring()
    
    # Update call duration display if call is connected
    if call_in_progress and call_status == "connected" and call_connect_time > 0:
        # Check if it's time to update (every 1 second)
        if not ticks_less(ticks_ms(), call_next_update):
            # Calculate actual elapsed time in seconds using ticks
            elapsed_ms = ticks_diff(ticks_ms(), call_connect_time)
            call_start_time = elapsed_ms // 1000  # Convert milliseconds to seconds
            update_call_status_display()
            # Set next update time (1 second from now)
            call_next_update = ticks_add(call_next_update, 1000)
