waterbearfieldschool/diy-phone/v9a/src/main.cpp

#include <Arduino.h>
#include <Adafruit_ST7735.h>
#include <Adafruit_GFX.h>
#include <SPI.h>

#define TFT_CS        A3
#define TFT_RST       12 // Or set to -1 and connect to Arduino RESET pin
#define TFT_DC        A5
  
void setup() {
  pinMode(LED_BUILTIN, OUTPUT);
}

void loop() {
  digitalWrite(LED_BUILTIN, HIGH);
  delay(1000);
  digitalWrite(LED_BUILTIN, LOW);
  delay(1000);
}
