waterbearfieldschool/diy-phone/testing/debounce.py

import board
import digitalio
from adafruit_debouncer import Debouncer

pin = digitalio.DigitalInOut(board.D9)
pin.direction = digitalio.Direction.INPUT
pin.pull = digitalio.Pull.UP
switch = Debouncer(pin)

while True:
    switch.update()
    if switch.fell:
        print('Just pressed')
    if switch.rose:
        print('Just released')
    if switch.value:
        print('not pressed')
    else:
        print('pressed')
